reading-hackspace/project-athena/Kicad/RLab Keyboard/ki-lime-pi-pico-2.1.2/_md-assets/images/footprints.png

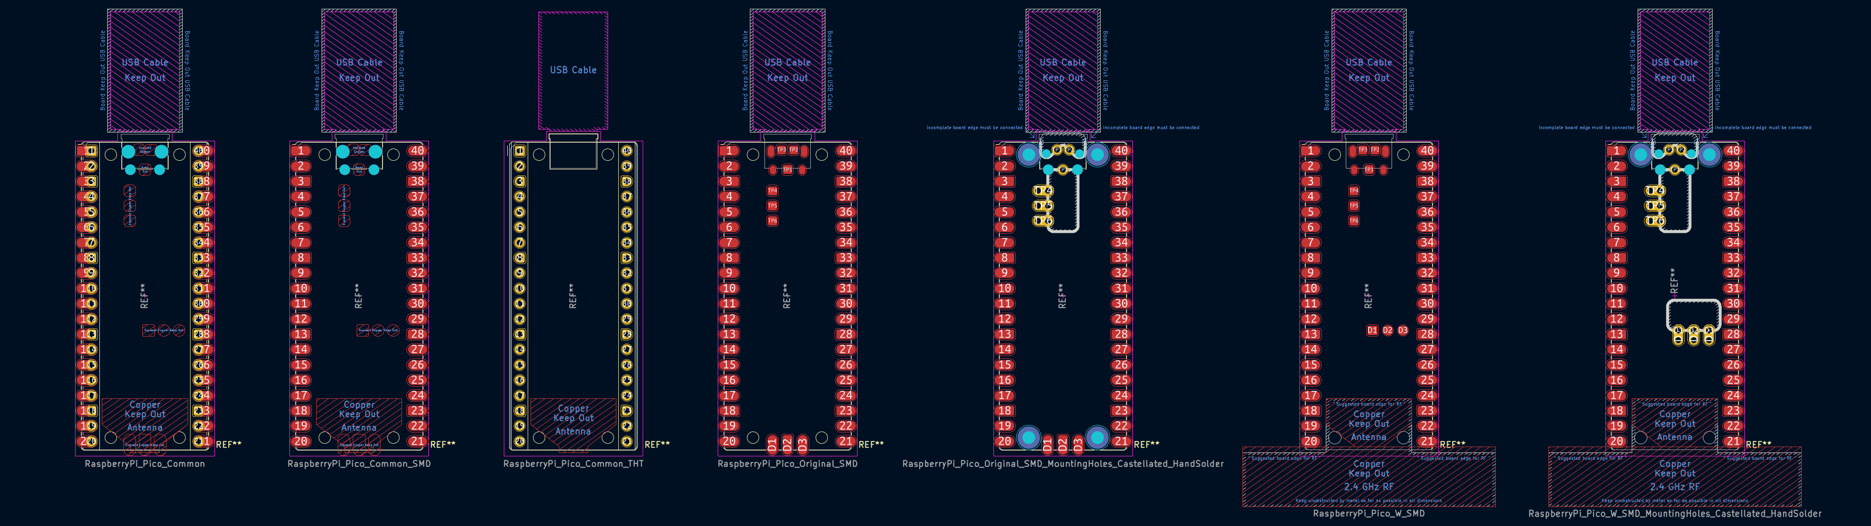
Kicad/RLab Keyboard/ki-lime-pi-pico-2.1.2/_md-assets/images/footprints.png
