reading-hackspace/project-athena/Kicad/RLab Keyboard/ki-lime-pi-pico-2.1.2/_md-assets/images/models.gif

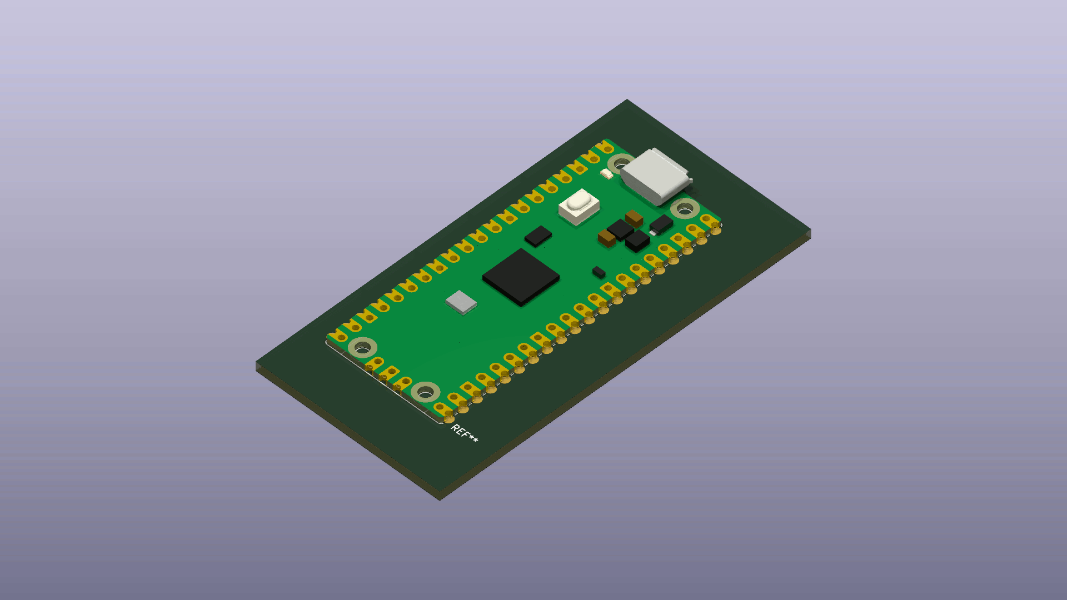
Kicad/RLab Keyboard/ki-lime-pi-pico-2.1.2/_md-assets/images/models.gif
