reading-hackspace/project-athena/Software/CircuitPython/I2C_Scanner.py

# Scanner i2c en MicroPython | MicroPython i2c scanner
# Renvoi l'adresse en decimal et hexa de chaque device connecte sur le bus i2c
# Return decimal and hexa adress of each i2c device
# https://projetsdiy.fr - https://diyprojects.io (dec. 2017)

import board
import busio

i2c = busio.I2C(board.GP5, board.GP4)
i2c.try_lock()
print('Scan i2c bus...')
devices = i2c.scan()

if len(devices) == 0:
  print("No i2c device !")
else:
  print('i2c devices found:',len(devices))

  for device in devices:  
    print("Decimal address: ",device," | Hexa address: ",hex(device))
i2c.unlock()
i2c.deinit()
